roxtastic/InkTimeRepo/Images/1.png

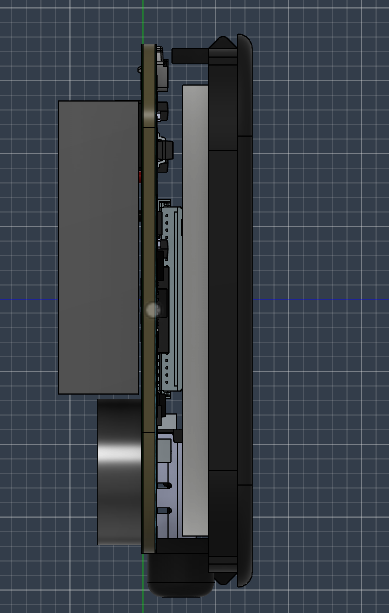
Images/1.png
