roxtastic/InkTimeRepo/Images/4.png

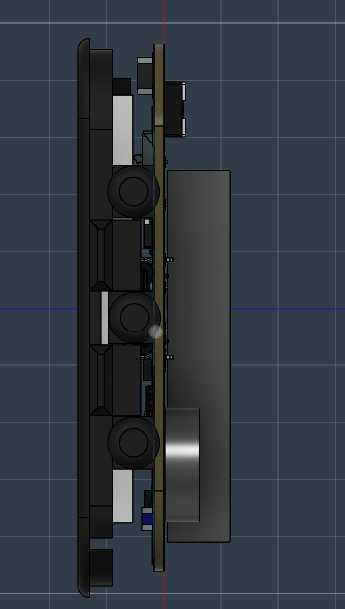
Images/4.png
